AidarIglesias/Projecte_Neteja_Parabrises/Simulacions/Driver Sensor Pluja/sim2.asc

R1: res; 10k
R2: res; {Pot}
R3: res; 10k
U1: TL081
V1: voltage; 5V
VSENSOR: voltage; PULSE(5 0 0 10u 10u 100u 200u 1)
Named nets: Vcc, 0, VSENSOR, Vout
.tran 0 150u 70u
.step dec param Pot 1k 100K
