AidarIglesias/Projecte_Neteja_Parabrises/Simulacions/Regulador/Regulador.asc

C1: cap; 1µ
C2: cap; 100n
C3: cap; 100n
C4: cap; 1µ
D1: diode; 1N914
D2: zener; BZX84C15L
U1: LT1117-5
VBAT: voltage; {V}
Named nets: 0, VCC, VBAT
.step param V list 9 10 11 12 13 14 15 16
.tran 1s
